ibrahim-albool/can-robust-industrial-card/Software/InputCard.X/src/ECAN1Drv.c

/**********************************************************************
* © 2005 Microchip Technology Inc.
*
* FileName:        main.c
* Dependencies:    Header (.h) files if applicable, see below
* Processor:       dsPIC33Fxxxx
* Compiler:        MPLAB® C30 v3.00 or higher
*
* SOFTWARE LICENSE AGREEMENT:
* Microchip Technology Incorporated ("Microchip") retains all ownership and 
* intellectual property rights in the code accompanying this message and in all 
* derivatives hereto.  You may use this code, and any derivatives created by 
* any person or entity by or on your behalf, exclusively with Microchip's
* proprietary products.  Your acceptance and/or use of this code constitutes 
* agreement to the terms and conditions of this notice.
*
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
* YOU ACKNOWLEDGE AND AGREE THAT, IN NO EVENT, SHALL MICROCHIP BE LIABLE, WHETHER 
* IN CONTRACT, WARRANTY, TORT (INCLUDING NEGLIGENCE OR BREACH OF STATUTORY DUTY), 
* STRICT LIABILITY, INDEMNITY, CONTRIBUTION, OR OTHERWISE, FOR ANY INDIRECT, SPECIAL, 
* PUNITIVE, EXEMPLARY, INCIDENTAL OR CONSEQUENTIAL LOSS, DAMAGE, FOR COST OR EXPENSE OF 
* ANY KIND WHATSOEVER RELATED TO THE CODE, HOWSOEVER CAUSED, EVEN IF MICROCHIP HAS BEEN 
* ADVISED OF THE POSSIBILITY OR THE DAMAGES ARE FORESEEABLE.  TO THE FULLEST EXTENT 
* ALLOWABLE BY LAW, MICROCHIP'S TOTAL LIABILITY ON ALL CLAIMS IN ANY WAY RELATED TO 
* THIS CODE, SHALL NOT EXCEED THE PRICE YOU PAID DIRECTLY TO MICROCHIP SPECIFICALLY TO 
* HAVE THIS CODE DEVELOPED.
*
* You agree that you are solely responsible for testing the code and 
* determining its suitability.  Microchip has no obligation to modify, test, 
* certify, or support the code.
*
* REVISION HISTORY:
*~~~~~~~~~~~~~~~~~~~~~~~~~~~~~~~~~~~~~~~~~~~~~~~~~~~~~~~~~~~~~~~~~~~~~~~~~~~~~~~~~~~~~~~~~~~~~~~~~
* Author          	Date      Comments on this revision
*~~~~~~~~~~~~~~~~~~~~~~~~~~~~~~~~~~~~~~~~~~~~~~~~~~~~~~~~~~~~~~~~~~~~~~~~~~~~~~~~~~~~~~~~~~~~~~~~~
* Vinaya Skanda 	10/18/06  First release of source file
* Vinaya Skanda		07/25/07  Updates from Joe Supinsky and Jatinder Gharoo incorporated
*~~~~~~~~~~~~~~~~~~~~~~~~~~~~~~~~~~~~~~~~~~~~~~~~~~~~~~~~~~~~~~~~~~~~~~~~~~~~~~~~~~~~~~~~~~~~~~~~~
*
* ADDITIONAL NOTES:
* This code is tested on Explorer-16 board with ECAN PICTail Card.
* The device used is dsPIC33FJ256GP710 controller 
*************************************************************************************************/


/* Device header file */
#if defined(__XC16__)
    #include <xc.h>
#elif defined(__C30__)
    #if defined(__dsPIC33E__)
    	#include <p33Exxxx.h>
    #elif defined(__dsPIC33F__)
    	#include <p33Fxxxx.h>
    #endif
#endif


#include <stdint.h>        /* Includes uint16_t definition                    */
#include <stdbool.h>       /* Includes true/false definition                  */

#include "../h/ECAN1Config.h"

/* 
This function configures Acceptance Filter "n" 

Inputs:
n-> Filter number [0-15]
identifier-> Bit ordering is given below
Filter Identifier (29-bits) : 0b000f ffff ffff ffff ffff ffff ffff ffff
								   |____________|_____________________|
									  SID10:0           EID17:0


Filter Identifier (11-bits) : 0b0000 0000 0000 0000 0000 0fff ffff ffff
														  |___________|
															  SID10:0
exide -> "0" for standard identifier 
		 "1" for Extended identifier

bufPnt -> Message buffer to store filtered message [0-15]
maskSel -> Optinal Masking of identifier bits [0-3]
						
*/

void ecan1WriteRxAcptFilter(int n, long identifier, unsigned int exide, unsigned int bufPnt,unsigned int maskSel) {

unsigned long sid10_0=0, eid15_0=0, eid17_16=0;
unsigned int *sidRegAddr,*bufPntRegAddr,*maskSelRegAddr, *fltEnRegAddr;


	C1CTRL1bits.WIN=1;

	// Obtain the Address of CiRXFnSID, CiBUFPNTn, CiFMSKSELn and CiFEN register for a given filter number "n"
	sidRegAddr = (unsigned int *)(&C1RXF0SID + (n << 1));
	bufPntRegAddr = (unsigned int *)(&C1BUFPNT1 + (n >> 2));
	maskSelRegAddr = (unsigned int *)(&C1FMSKSEL1 + (n >> 3));
	fltEnRegAddr = (unsigned int *)(&C1FEN1);


	// Bit-filed manupulation to write to Filter identifier register
	if(exide==1) { 	// Filter Extended Identifier
		eid15_0 = (identifier & 0xFFFF);
		eid17_16= (identifier>>16) & 0x3;
		sid10_0 = (identifier>>18) & 0x7FF;

		*sidRegAddr=(((sid10_0)<<5) + 0x8) + eid17_16;	// Write to CiRXFnSID Register
	    *(sidRegAddr+1)= eid15_0;					// Write to CiRXFnEID Register

	}else{			// Filter Standard Identifier
		sid10_0 = (identifier & 0x7FF);			
		*sidRegAddr=(sid10_0)<<5;					// Write to CiRXFnSID Register
		*(sidRegAddr+1)=0;							// Write to CiRXFnEID Register
	}


   *bufPntRegAddr = (*bufPntRegAddr) & (0xFFFF - (0xF << (4 *(n & 3)))); // clear nibble
   *bufPntRegAddr = ((bufPnt << (4 *(n & 3))) | (*bufPntRegAddr));       // Write to C1BUFPNTn Register

   *maskSelRegAddr = (*maskSelRegAddr) & (0xFFFF - (0x3 << ((n & 7) * 2))); // clear 2 bits
   *maskSelRegAddr = ((maskSel << (2 * (n & 7))) | (*maskSelRegAddr));      // Write to C1FMSKSELn Register

   *fltEnRegAddr = ((0x1 << n) | (*fltEnRegAddr)); // Write to C1FEN1 Register

   C1CTRL1bits.WIN=0;


}


/* 
This function configures Acceptance Filter Mask "m" 

Inputs:
m-> Mask number [0-2]
identifier-> Bit ordering is given below
Filter Mask Identifier (29-bits) : 0b000f ffff ffff ffff ffff ffff ffff ffff
								        |____________|_____________________|
									        SID10:0           EID17:0


Filter Mask Identifier (11-bits) : 0b0000 0000 0000 0000 0000 0fff ffff ffff
														       |___________|
															      SID10:0

mide ->  "0"  Match either standard or extended address message if filters match 
         "1"  Match only message types that correpond to 'exide' bit in filter
					
*/

void ecan1WriteRxAcptMask(int m, long identifier, unsigned int mide, unsigned int exide){

unsigned long sid10_0=0, eid15_0=0, eid17_16=0;
unsigned int *maskRegAddr;


	C1CTRL1bits.WIN=1;

	// Obtain the Address of CiRXMmSID register for given Mask number "m"
	maskRegAddr = (unsigned int *)(&C1RXM0SID + (m << 1));

	// Bit-filed manupulation to write to Filter Mask register
	if(exide==1) 
	{ 	// Filter Extended Identifier
		eid15_0 = (identifier & 0xFFFF);
		eid17_16= (identifier>>16) & 0x3;
		sid10_0 = (identifier>>18) & 0x7FF;

		if(mide==1)
			*maskRegAddr=((sid10_0)<<5) + 0x0008 + eid17_16;	// Write to CiRXMnSID Register
		else
			*maskRegAddr=((sid10_0)<<5) + eid17_16;	// Write to CiRXMnSID Register
	    *(maskRegAddr+1)= eid15_0;					// Write to CiRXMnEID Register

	}
	else
	{			// Filter Standard Identifier
		sid10_0 = (identifier & 0x7FF);			
		if(mide==1)
			*maskRegAddr=((sid10_0)<<5) + 0x0008;					// Write to CiRXMnSID Register
		else
			*maskRegAddr=(sid10_0)<<5;					// Write to CiRXMnSID Register	
		
		*(maskRegAddr+1)=0;							// Write to CiRXMnEID Register
	}


	C1CTRL1bits.WIN=0;	

}


/* ECAN Transmit Message Buffer Configuration

Inputs:
buf	-> Transmit Buffer Number

txIdentifier ->	


Extended Identifier (29-bits) : 0b000f ffff ffff ffff ffff ffff ffff ffff
								     |____________|_____________________|
									        SID10:0           EID17:0


Standard Identifier (11-bits) : 0b0000 0000 0000 0000 0000 0fff ffff ffff
														    |___________|
															      SID10:0

Standard Message Format: 
											Word0 : 0b000f ffff ffff ffff
													     |____________|||___
 									        				SID10:0   SRR   IDE     

											Word1 : 0b0000 0000 0000 0000
														   |____________|
															  EID17:6

											Word2 : 0b0000 00f0 0000 ffff
													  |_____||	  	 |__|
													  EID5:0 RTR   	  DLC
										
																  
																	
Extended Message Format: 
											Word0 : 0b000f ffff ffff ffff
													     |____________|||___
 									        				SID10:0   SRR   IDE     

											Word1 : 0b0000 ffff ffff ffff
														   |____________|
															  EID17:6

											Word2 : 0bffff fff0 0000 ffff
													  |_____||	  	 |__|
													  EID5:0 RTR   	  DLC

ide -> "0"  Message will transmit standard identifier
	   "1"  Message will transmit extended identifier



remoteTransmit -> "0" Message transmitted is a normal message
				  "1" Message transmitted is a remote message

				Standard Message Format: 
											Word0 : 0b000f ffff ffff ff1f
													     |____________|||___
 									        				SID10:0   SRR   IDE     

											Word1 : 0b0000 0000 0000 0000
														   |____________|
															  EID17:6

											Word2 : 0b0000 0010 0000 ffff
													  |_____||	  	 |__|
													  EID5:0 RTR   	  DLC
										
																  
																	
				Extended Message Format: 
											Word0 : 0b000f ffff ffff ff1f
													     |____________|||___
 									        				SID10:0   SRR   IDE     

											Word1 : 0b0000 ffff ffff ffff
														   |____________|
															  EID17:6

											Word2 : 0bffff ff10 0000 ffff
													  |_____||	  	 |__|
													  EID5:0 RTR   	  DLC

*/

void ecan1WriteTxMsgBufId(unsigned int buf, long txIdentifier, unsigned int ide, unsigned int remoteTransmit){

unsigned long word0=0, word1=0, word2=0;
unsigned long sid10_0=0, eid5_0=0, eid17_6=0;


if(ide)
	{
		eid5_0  = (txIdentifier & 0x3F);
		eid17_6 = (txIdentifier>>6) & 0xFFF;
		sid10_0 = (txIdentifier>>18) & 0x7FF;
		word1 = eid17_6;
	}
	else
	{
		sid10_0 = (txIdentifier & 0x7FF);
	}
	
	
	if(remoteTransmit==1) { 	// Transmit Remote Frame

		word0 = ((sid10_0 << 2) | ide | 0x2);
		word2 = ((eid5_0 << 10)| 0x0200);}

	else {
		
		word0 = ((sid10_0 << 2) | ide);
		word2 = (eid5_0 << 10);
	     }
			
// Obtain the Address of Transmit Buffer in DMA RAM for a given Transmit Buffer number

if(ide)
	ecan1msgBuf[buf][0] = (word0 | 0x0002);
else
	ecan1msgBuf[buf][0] = word0;

	ecan1msgBuf[buf][1] = word1;
	ecan1msgBuf[buf][2] = word2;
}


/* ECAN Transmit Data

Inputs :
buf -> Transmit Buffer Number

dataLength -> Length of Data in Bytes to be transmitted

data1/data2/data3/data4 ->  Transmit Data Bytes 

*/

void ecan1WriteTxMsgBufData(unsigned int buf, unsigned int dataLength, unsigned int data1, unsigned int data2, unsigned int data3, unsigned int data4){

	ecan1msgBuf[buf][2] = ((ecan1msgBuf[buf][2] & 0xFFF0) + dataLength) ;
	
	ecan1msgBuf[buf][3] = data1;
	ecan1msgBuf[buf][4] = data2;
	ecan1msgBuf[buf][5] = data3;
	ecan1msgBuf[buf][6] = data4;

}

/*------------------------------------------------------------------------------
 * Disable RX Acceptance Filter
 * void ecan1DisableRXFilter(int n)
 *------------------------------------------------------------------------------
 *
 n -> Filter number [0-15]
*/

void ecan1DisableRXFilter(int n)
{
unsigned int *fltEnRegAddr;
   C1CTRL1bits.WIN=1;
   fltEnRegAddr = (unsigned int *)(&C1FEN1);
   *fltEnRegAddr = (*fltEnRegAddr) & (0xFFFF - (0x1 << n));
   C1CTRL1bits.WIN=0;

}
