ibrahim-albool/can-robust-industrial-card/Software/InputCard.X/src/system.c

/******************************************************************************/
/* Files to Include                                                           */
/******************************************************************************/

/* Device header file */
#if defined(__XC16__)
    #include <xc.h>
#elif defined(__C30__)
    #if defined(__dsPIC33E__)
    	#include <p33Exxxx.h>
    #elif defined(__dsPIC33F__)
    	#include <p33Fxxxx.h>
    #endif
#endif


#include <stdint.h>          /* For uint16_t definition                       */
#include <stdbool.h>         /* For true/false definition                     */

#include "../h/system.h"          /* variables/params used by system.c             */

/******************************************************************************/
/* System Level Functions                                                     */
/*                                                                            */
/* Custom oscillator configuration funtions, reset source evaluation          */
/* functions, and other non-peripheral microcontroller initialization         */
/* functions get placed in system.c.                                          */
/*                                                                            */
/******************************************************************************/

/* Refer to the device Family Reference Manual Oscillator section for
information about available oscillator configurations.  Typically
this would involve configuring the oscillator tuning register or clock
switching useing the compiler's __builtin_write_OSCCON functions.
Refer to the C Compiler for PIC24 MCUs and dsPIC DSCs User Guide in the
compiler installation directory /doc folder for documentation on the
__builtin functions.*/

/* TODO Add clock switching code if appropriate.  An example stub is below.   */
void configureOscillator(void){

/*  Configure Oscillator to operate the device at 40Mhz
 	Fosc= Fin*M/(N1*N2), Fcy=Fosc/2
 	Fosc= 8M*40/(2*2)=80Mhz for 8M input clock */

	PLLFBD=38;					/* M=40 */
	CLKDIVbits.PLLPOST=0;		/* N1=2 */
	CLKDIVbits.PLLPRE=0;		/* N2=2 */
	OSCTUN=0;					/* Tune FRC oscillator, if FRC is used */

/* Disable Watch Dog Timer */

	RCONbits.SWDTEN=0;

/* Clock switch to incorporate PLL*/
	__builtin_write_OSCCONH(0x03);		// Initiate Clock Switch to Primary
													// Oscillator with PLL (NOSC=0b011)
	__builtin_write_OSCCONL(0x01);		// Start clock switching
	while (OSCCONbits.COSC != 0b011);	// Wait for Clock switch to occur	


/* Wait for PLL to lock */

	while(OSCCONbits.LOCK!=1) {};
}



void clearIntrflags(void){
/* Clear Interrupt Flags */

	IFS0=0;
	IFS1=0;
	IFS2=0;
	IFS3=0;
	IFS4=0;
}
